geckopfote/keyrigami/showcase/IMG_20170914_121415_301.jpg

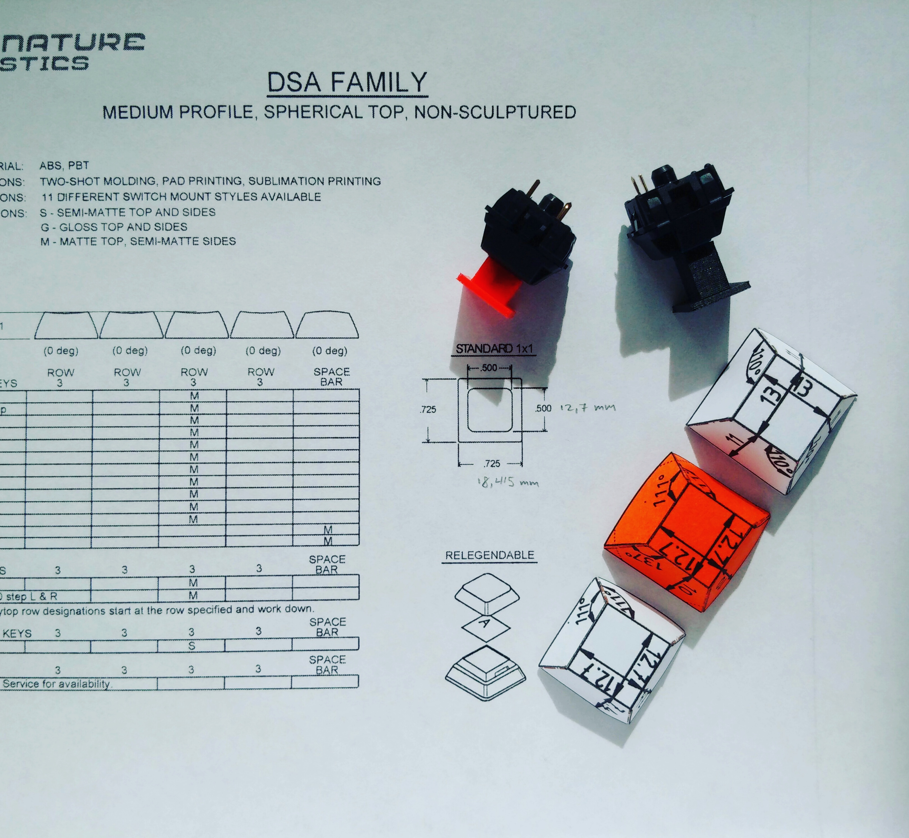
showcase/IMG_20170914_121415_301.jpg
