geckopfote/keyrigami/showcase/IMG_20171126_0948504.jpg

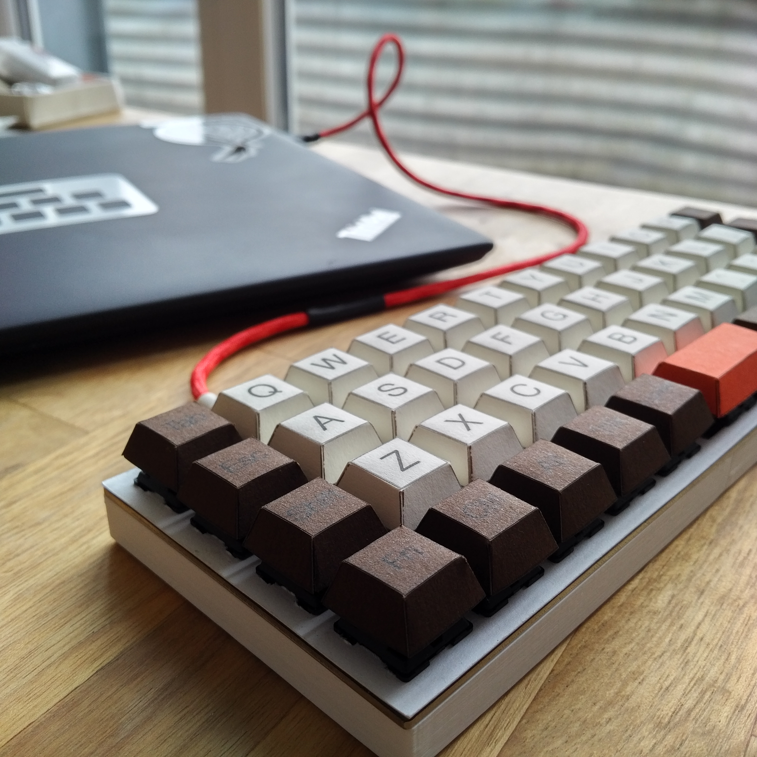
showcase/IMG_20171126_0948504.jpg
